BrownSpaceEngineering/PVDX-Burn-Wire/LTSpice_burnWire.asc

Burn_Wire: res; 1
C1: cap; 0.1µF
C2: cap; 47µF
C3: cap; 47µF
C4: cap; 47µ; V=10 Irms=0 Rser=0 Lser=0 mfg="Murata" pn="GRM32ER71A476ME15" type="X7R"
C5: cap; 22µF
D1: diode
L1: ind; 3.3µH; Rser=1m
R1: res; 10k
R2: res; 0.5
R3: res; 10k
U1: ADP2303
V1: voltage; 8
Named nets: 0, burn_pos
.tran 0 20m 0 20n
